rodan/solar-charger/firmware/rev4.1/rtc.c

/*
    rtca.c: TI CC430 Hardware Realtime Clock (RTC_A)

    Copyright (C) 2011-2012 Angelo Arrifano <miknix@gmail.com>

				http://www.openchronos-ng.sourceforge.net

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
    You should have received a copy of the GNU General Public License
    along with this program.  If not, see <http://www.gnu.org/licenses/>.
*/

#include <inttypes.h>
#include "rtc.h"
#include "rtca_now.h"

#ifdef CONFIG_RTC_DST
#include "rtc_dst.h"
#endif

volatile enum rtca_tevent rtca_last_event;
static struct rtca_tm rtca_time;

void rtca_init(void)
{
    rtca_time.year = COMPILE_YEAR;
    rtca_time.mon = COMPILE_MON;
    rtca_time.day = COMPILE_DAY;
    rtca_time.dow = COMPILE_DOW;
    rtca_time.hour = COMPILE_HOUR;
    rtca_time.min = COMPILE_MIN;
    rtca_time.sec = 57; // minute irq will happen 3s after uC start

    RTCCTL01 |= RTCMODE | RTCRDYIE | RTCTEVIE;
    rtca_set_time(&rtca_time);

#ifdef CONFIG_RTC_DST
    rtc_dst_init();
#endif

}

void rtca_set_time(struct rtca_tm *t)
{
    rtca_stop();

    RTCSEC = t->sec;
    RTCMIN = t->min;
    RTCHOUR = t->hour;
    RTCDAY = t->day;
    RTCDOW = t->dow;
    RTCMON = t->mon;
    RTCYEARL = t->year & 0xff;
    RTCYEARH = t->year >> 8;

    rtca_start();
}

void rtca_get_time(struct rtca_tm *t)
{
    t->sys = rtca_time.sys;
    t->sec = rtca_time.sec;
    t->min = rtca_time.min;
    t->hour = rtca_time.hour;
    t->day = rtca_time.day;
    t->dow = rtca_time.dow;
    t->mon = rtca_time.mon;
    t->year = rtca_time.year;
}

uint8_t rtca_get_event(void)
{
    return rtca_last_event;
}

void rtca_rst_event(void)
{
    rtca_last_event = RTCA_EV_NONE;
}

void rtca_get_alarm(struct rtca_tm *t, uint8_t *ae_flags)
{
    *ae_flags = 0;
    t->min = RTCAMIN & 0x7f;
    t->hour = RTCAHOUR & 0x7f;
    t->day = RTCADAY & 0x7f;
    t->dow = RTCADOW & 0x7f;

    if (RTCAMIN & RTCAE) {
        *ae_flags |= AE_MIN;
    }
    if (RTCAHOUR & RTCAE) {
        *ae_flags |= AE_HOUR;
    }
    if (RTCADAY & RTCAE) {
        *ae_flags |= AE_DAY;
    }
    if (RTCADOW & RTCAE) {
        *ae_flags |= AE_DOW;
    }
}

void rtca_set_alarm(struct rtca_tm *t, const uint8_t ae_flags)
{
    uint16_t reg = RTCCTL01;
    RTCCTL01 &= ~(RTCAIE | RTCAIFG);

    if (ae_flags & AE_MIN) {
        RTCAMIN = RTCAE | t->min;
    } else {
        RTCAMIN = 0;
    }

    if (ae_flags & AE_HOUR) {
        RTCAHOUR = RTCAE | t->hour;
    } else {
        RTCAHOUR = 0;
    }

    if (ae_flags & AE_DAY) {
        RTCADAY = RTCAE | t->day;
    } else {
        RTCADAY = 0;
    }

    if (ae_flags & AE_DOW) {
        RTCADOW = RTCAE | t->dow;
    } else {
        RTCADOW = 0;
    }

    RTCCTL01 = reg;
}

void rtca_enable_alarm()
{
    RTCCTL01 &= ~(RTCAIFG);
    RTCCTL01 |= RTCAIE;
}

void rtca_disable_alarm()
{
    RTCCTL01 &= ~RTCAIE;
    RTCAHOUR &= ~RTCAE;
    RTCAMIN &= ~RTCAE;
}

__attribute__((interrupt(RTC_VECTOR)))
void RTC_A_ISR(void)
{
    uint16_t iv = RTCIV;

    rtca_time.sec = RTCSEC;

    rtca_time.sys++;

    enum rtca_tevent ev = 0;

    if (iv == RTCIV_RTCRDYIFG) {
        ev = RTCA_EV_SECOND;
        goto finish;
    }

    if (iv == RTCIV_RTCAIFG) {
        sig0_on;
        ev = RTCA_EV_ALARM;
        goto finish;
    }

    {
        if (iv != RTCIV_RTCTEVIFG)
            goto finish;

        ev |= RTCA_EV_MINUTE;
        rtca_time.min = RTCMIN;

        if (rtca_time.min != 0)
            goto finish;

        ev |= RTCA_EV_HOUR;
        rtca_time.hour = RTCHOUR;

#ifdef CONFIG_RTC_DST
        rtc_dst_hourly_update();
#endif

        if (rtca_time.hour != 0)
            goto finish;

        ev |= RTCA_EV_DAY;
        rtca_time.day = RTCDAY;
        rtca_time.dow = RTCDOW;

        if (rtca_time.day != 1)
            goto finish;

        ev |= RTCA_EV_MONTH;
        rtca_time.mon = RTCMON;

        if (rtca_time.mon != 1)
            goto finish;

        ev |= RTCA_EV_YEAR;
        rtca_time.year = RTCYEARL | (RTCYEARH << 8);
#ifdef CONFIG_RTC_DST
        rtc_dst_calculate_dates(rtca_time.year, rtca_time.mon, rtca_time.day, rtca_time.hour);
#endif
    }

 finish:
    rtca_last_event |= ev;

    _BIC_SR_IRQ(LPM3_bits);
}
